picass02005/Buzzer-Insagora/CAO/PCB/kicad_project/footprints/ESP32-DEVKIT-V1/ESP32-DEVKIT-V1.step

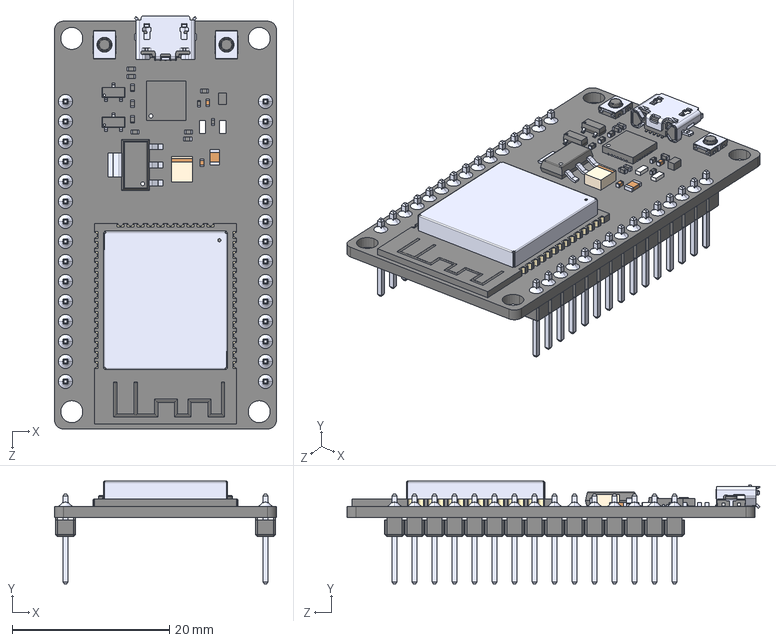
[picture p15: CAD file, 2026-02-16]
CAO/PCB/kicad_project/footprints/ESP32-DEVKIT-V1/ESP32-DEVKIT-V1.step
28.2 x 13.1 x 52.5 mm
