picass02005/Buzzer-Insagora/esp/pins.h

/*
 * Copyright (c) 2025 picasso2005 <clementduran0@gmail.com>
 *
 * This software is released under the MIT License.
 * https://opensource.org/licenses/MIT
 */

#ifndef PINS_H
#define PINS_H

#define BUTTON 5      // Button is normally closed
#define ONBOARD_LED 2 // Onboard LED
#define LED_STRIP 15  // LED strip pin
#define LED_NB 20      // Number of LED

// #define DEBUG  // Allow serial port prints

#endif
