picass02005/Buzzer-Insagora/esp/cmd-led.h

/*
 * Copyright (c) 2025 picasso2005 <clementduran0@gmail.com>
 *
 * This software is released under the MIT License.
 * https://opensource.org/licenses/MIT
 */

#ifndef CMD_LED_H
#define CMD_LED_H

#include "esp-now.h"

void setup_led();
void led_welcome_animation();

void led_bluetooth_connect();
void led_bluetooth_disconnect();
void led_master();

void set_led_cmd(ESPNowMessage msg);
void clear_led_cmd(ESPNowMessage msg);
void get_led_nb_cmd(ESPNowMessage msg);

#endif
